WillDoesBuild/ISS-tracker/Prusa Project Files/InsideMagnet.3mf

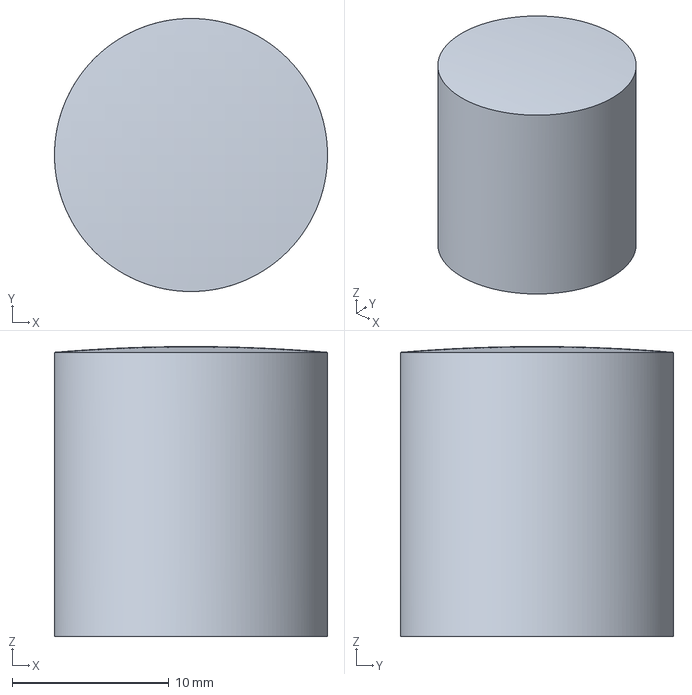
[picture p12: CAD file, 2025-07-25]
Prusa Project Files/InsideMagnet.3mf
17.4 x 17.4 x 18.5 mm
